trollectronics/trollbook/src/common/terminal/src/vgafont.c

#include <stdint.h>

uint8_t vgafont_data[2672] = {
	0, 0, 0, 0, 0, 0, 0, 0, 0, 0, 0, 0, 0, 0, 0, 0,
	0, 24, 102, 66, 66, 165, 129, 165, 90, 66, 102, 24, 0, 0, 0, 0,
	0, 24, 126, 126, 126, 219, 255, 219, 102, 126, 126, 24, 0, 0, 0, 0,
	0, 0, 0, 0, 0, 68, 238, 254, 124, 124, 56, 16, 0, 0, 0, 0,
	0, 0, 0, 0, 0, 16, 56, 124, 254, 124, 56, 16, 0, 0, 0, 0,
	0, 0, 0, 0, 0, 16, 56, 84, 238, 108, 16, 56, 0, 0, 0, 0,
	0, 0, 0, 0, 0, 16, 56, 124, 254, 124, 16, 56, 0, 0, 0, 0,
	0, 0, 0, 0, 0, 0, 16, 56, 124, 56, 16, 0, 0, 0, 0, 0,
	255, 255, 255, 255, 255, 255, 239, 199, 131, 199, 239, 255, 255, 255, 255, 255,
	0, 0, 0, 0, 0, 16, 108, 68, 130, 68, 108, 16, 0, 0, 0, 0,
	255, 255, 255, 255, 255, 239, 147, 187, 125, 187, 147, 239, 255, 255, 255, 255,
	0, 224, 192, 160, 16, 56, 68, 130, 130, 130, 68, 56, 0, 0, 0, 0,
	0, 56, 68, 130, 130, 130, 68, 56, 16, 16, 56, 16, 0, 0, 0, 0,
	0, 48, 208, 48, 208, 16, 16, 16, 28, 30, 30, 12, 0, 0, 0, 0,
	64, 160, 208, 168, 152, 136, 136, 232, 254, 255, 111, 6, 0, 0, 0, 0,
	0, 0, 0, 0, 0, 16, 84, 40, 198, 40, 84, 16, 0, 0, 0, 0,
	0, 2, 6, 14, 30, 62, 126, 62, 30, 14, 6, 2, 0, 0, 0, 0,
	0, 128, 192, 224, 240, 248, 252, 248, 240, 224, 192, 128, 0, 0, 0, 0,
	0, 16, 56, 124, 16, 16, 16, 16, 16, 124, 56, 16, 0, 0, 0, 0,
	0, 68, 68, 68, 68, 68, 68, 68, 68, 0, 0, 68, 0, 0, 0, 0,
	0, 248, 164, 162, 162, 162, 164, 184, 160, 160, 160, 160, 0, 0, 0, 0,
	0, 56, 68, 130, 18, 42, 68, 168, 144, 130, 68, 56, 0, 0, 0, 0,
	0, 0, 0, 0, 0, 0, 0, 0, 254, 254, 254, 254, 0, 0, 0, 0,
	0, 16, 56, 124, 16, 16, 16, 16, 16, 124, 56, 16, 124, 0, 0, 0,
	0, 16, 56, 124, 16, 16, 16, 16, 16, 16, 16, 16, 0, 0, 0, 0,
	0, 16, 16, 16, 16, 16, 16, 16, 16, 124, 56, 16, 0, 0, 0, 0,
	0, 0, 0, 0, 32, 96, 254, 96, 32, 0, 0, 0, 0, 0, 0, 0,
	0, 0, 0, 0, 8, 12, 254, 12, 8, 0, 0, 0, 0, 0, 0, 0,
	0, 0, 0, 0, 0, 0, 0, 0, 0, 2, 2, 254, 0, 0, 0, 0,
	0, 0, 0, 0, 40, 108, 254, 108, 40, 0, 0, 0, 0, 0, 0, 0,
	0, 16, 56, 124, 254, 0, 0, 0, 0, 0, 0, 0, 0, 0, 0, 0,
	0, 0, 0, 0, 0, 0, 0, 0, 254, 124, 56, 16, 0, 0, 0, 0,
	0, 0, 0, 0, 0, 0, 0, 0, 0, 0, 0, 0, 0, 0, 0, 0,
	0, 16, 16, 16, 16, 16, 16, 16, 16, 0, 0, 16, 0, 0, 0, 0,
	0, 68, 68, 34, 0, 0, 0, 0, 0, 0, 0, 0, 0, 0, 0, 0,
	0, 0, 0, 0, 36, 36, 255, 36, 36, 255, 36, 36, 0, 0, 0, 0,
	16, 56, 84, 146, 18, 20, 56, 80, 144, 146, 84, 56, 16, 0, 0, 0,
	0, 64, 64, 32, 34, 21, 18, 72, 168, 68, 4, 2, 2, 0, 0, 0,
	0, 0, 0, 12, 18, 18, 12, 82, 33, 33, 82, 140, 0, 0, 0, 0,
	0, 32, 32, 16, 0, 0, 0, 0, 0, 0, 0, 0, 0, 0, 0, 0,
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
};
