trollectronics/trollbook/src/common/terminal/src/smallfont.c

#include <stdint.h>
#include <stddef.h>

uint8_t smallfont_data[] = {
	0x00, 0x00, 0x00, 0x00, 0x00, 0x00, 0x00, 0x00, 0x00, 0x00, 0x00, 0x00,
	0x00, 0x00, 0x00, 0x00, 0x00, 0x00, 0x00, 0x00, 0x00, 0x00, 0x00, 0x00,
	0x00, 0x00, 0x00, 0x00, 0x00, 0x00, 0x00, 0x00, 0x00, 0x00, 0x00, 0x00,
	0x00, 0x00, 0x00, 0x00, 0x00, 0x00, 0x00, 0x00, 0x00, 0x00, 0x00, 0x00,
	0x00, 0x00, 0x00, 0x00, 0x00, 0x00, 0x00, 0x00, 0x00, 0x00, 0x00, 0x00,
	0x00, 0x00, 0x00, 0x00, 0x00, 0x00, 0x00, 0x00, 0x00, 0x00, 0x00, 0x00,
	0x00, 0x00, 0x00, 0x00, 0x00, 0x00, 0x00, 0x00, 0x00, 0x00, 0x00, 0x00,
	0x00, 0x00, 0x00, 0x00, 0x00, 0x00, 0x00, 0x00, 0x00, 0x00, 0x00, 0x00,
	0x00, 0x00, 0x00, 0x00, 0x00, 0x00, 0x00, 0x00, 0x00, 0x00, 0x00, 0x00,
	0x00, 0x00, 0x00, 0x00, 0x00, 0x00, 0x00, 0x00, 0x00, 0x00, 0x00, 0x00,
	0x00, 0x00, 0x00, 0x00, 0x00, 0x00, 0x00, 0x00, 0x00, 0x00, 0x00, 0x00,
	0x00, 0x00, 0x00, 0x00, 0x00, 0x00, 0x00, 0x00, 0x00, 0x00, 0x00, 0x00,
	0x00, 0x00, 0x00, 0x00, 0x00, 0x00, 0x00, 0x00, 0x00, 0x00, 0x00, 0x00,
	0x00, 0x00, 0x00, 0x00, 0x00, 0x00, 0x00, 0x00, 0x00, 0x00, 0x00, 0x00,
	0x00, 0x00, 0x00, 0x00, 0x00, 0x00, 0x00, 0x00, 0x00, 0x00, 0x00, 0x00,
	0x00, 0x00, 0x00, 0x00, 0x00, 0x00, 0x00, 0x00, 0x00, 0x00, 0x00, 0x00,
	0x00, 0x00, 0x00, 0x00, 0x00, 0x00, 0x00, 0x00, 0x00, 0x00, 0x00, 0x00,
	0x00, 0x00, 0x00, 0x00, 0x00, 0x00, 0x00, 0x00, 0x00, 0x00, 0x00, 0x00,
	0x00, 0x00, 0x00, 0x00, 0x00, 0x00, 0x00, 0x00, 0x00, 0x00, 0x00, 0x00,
	0x00, 0x00, 0x00, 0x00, 0x00, 0x00, 0x00, 0x00, 0x00, 0x00, 0x00, 0x00,
	0x00, 0x00, 0x00, 0x00, 0x00, 0x00, 0x00, 0x00, 0x00, 0x00, 0x00, 0x00,
	0x00, 0x00, 0x00, 0x00, 0x00, 0x00, 0x00, 0x00, 0x00, 0x00, 0x00, 0x00,
	0x00, 0x08, 0x08, 0x08, 0x08, 0x00, 0x08, 0x00, 0x28, 0x28, 0x14, 0x00,
	0x00, 0x00, 0x00, 0x00, 0x00, 0x24, 0x7e, 0x24, 0x24, 0x7e, 0x24, 0x00,
	0x08, 0x1c, 0x2a, 0x0c, 0x18, 0x2a, 0x1c, 0x08, 0x00, 0x46, 0x26, 0x10,
	0x08, 0x64, 0x62, 0x00, 0x00, 0x0c, 0x12, 0x0c, 0x52, 0x32, 0x4c, 0x00,
	0x10, 0x10, 0x08, 0x00, 0x00, 0x00, 0x00, 0x00, 0x10, 0x08, 0x08, 0x08,
	0x08, 0x08, 0x08, 0x10, 0x08, 0x10, 0x10, 0x10, 0x10, 0x10, 0x10, 0x08,
	0x00, 0x2a, 0x1c, 0x3e, 0x1c, 0x2a, 0x00, 0x00, 0x00, 0x08, 0x08, 0x3e,
	0x08, 0x08, 0x00, 0x00, 0x00, 0x00, 0x00, 0x00, 0x00, 0x10, 0x10, 0x08,
	0x00, 0x00, 0x00, 0x3e, 0x00, 0x00, 0x00, 0x00, 0x00, 0x00, 0x00, 0x00,
	0x00, 0x10, 0x10, 0x00, 0x00, 0x40, 0x20, 0x10, 0x08, 0x04, 0x02, 0x00,
	0x1c, 0x22, 0x22, 0x2a, 0x22, 0x22, 0x1c, 0x00, 0x08, 0x0c, 0x08, 0x08,
	0x08, 0x08, 0x1c, 0x00, 0x18, 0x24, 0x20, 0x10, 0x08, 0x04, 0x3c, 0x00,
	0x18, 0x24, 0x20, 0x18, 0x20, 0x24, 0x18, 0x00, 0x10, 0x14, 0x14, 0x3c,
	0x10, 0x10, 0x10, 0x00, 0x3c, 0x04, 0x18, 0x20, 0x20, 0x24, 0x18, 0x00,
	0x18, 0x24, 0x04, 0x1c, 0x24, 0x24, 0x18, 0x00, 0x3c, 0x20, 0x20, 0x10,
	0x10, 0x08, 0x08, 0x00, 0x18, 0x24, 0x24, 0x18, 0x24, 0x24, 0x18, 0x00,
	0x18, 0x24, 0x24, 0x38, 0x20, 0x20, 0x20, 0x00, 0x00, 0x08, 0x08, 0x00,
	0x00, 0x08, 0x08, 0x00, 0x00, 0x08, 0x08, 0x00, 0x00, 0x08, 0x08, 0x04,
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
};
size_t smallfont_len = 1024;
