trollectronics/trollbook/src/common/peripheral/include/spi.h

#ifndef _SPI_H_
#define _SPI_H_
#include <stdint.h>
#include "peripheral.h"

#define SPI_REG_DATA *((volatile uint32_t *) (PERIPHERAL_SPI_BASE + 0x0))
#define SPI_REG_STATUS *((volatile uint32_t *) (PERIPHERAL_SPI_BASE + 0x4))
#define SPI_REG_SS *((volatile uint32_t *) (PERIPHERAL_SPI_BASE + 0x8))

typedef enum SpiSlave SpiSlave;

enum SpiSlave {
	SPI_SLAVE_NONE,
	SPI_SLAVE_ROM,
	SPI_SLAVE_KBD,
	SPI_SLAVE_SD,
	SPI_SLAVE_EXT0,
	SPI_SLAVE_EXT1,
	SPI_SLAVE_EXT2,
	SPI_SLAVE_EXT3,
};

void spi_select_slave(int slave);
uint8_t spi_send_recv(uint8_t dat);
void spi_set_clockdiv(uint16_t clkdiv);
uint16_t spi_get_clockdiv();

#endif
